evezor/v0_4x_relay_board/pics/20201109_051040.jpg

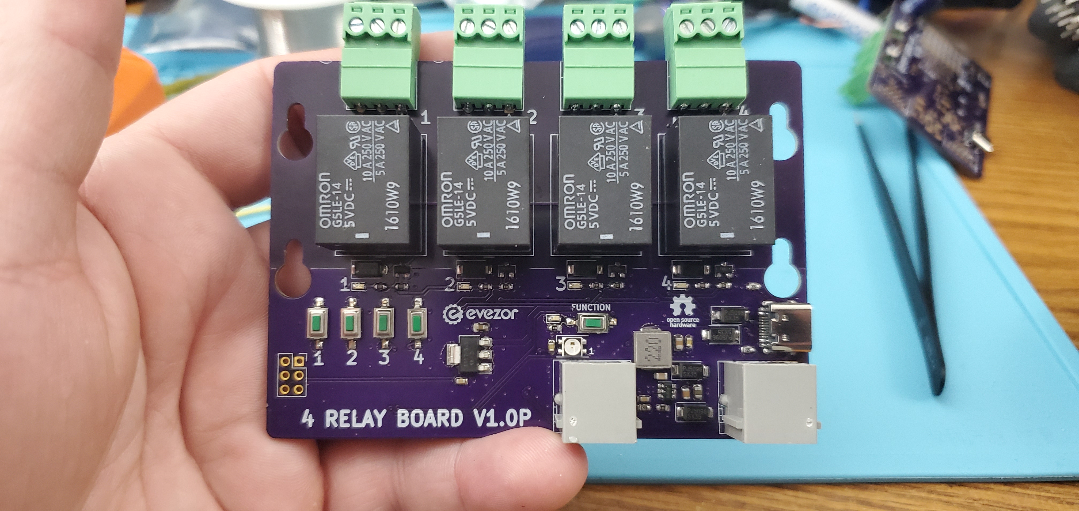
pics/20201109_051040.jpg
